JuanAVillagomez/FPGA-Retro-Arcade-Console/hardware/Retro_KiCAD.kicad_sch

## KiCad design hardware/Retro_KiCAD.kicad_sch (2026-09-01)

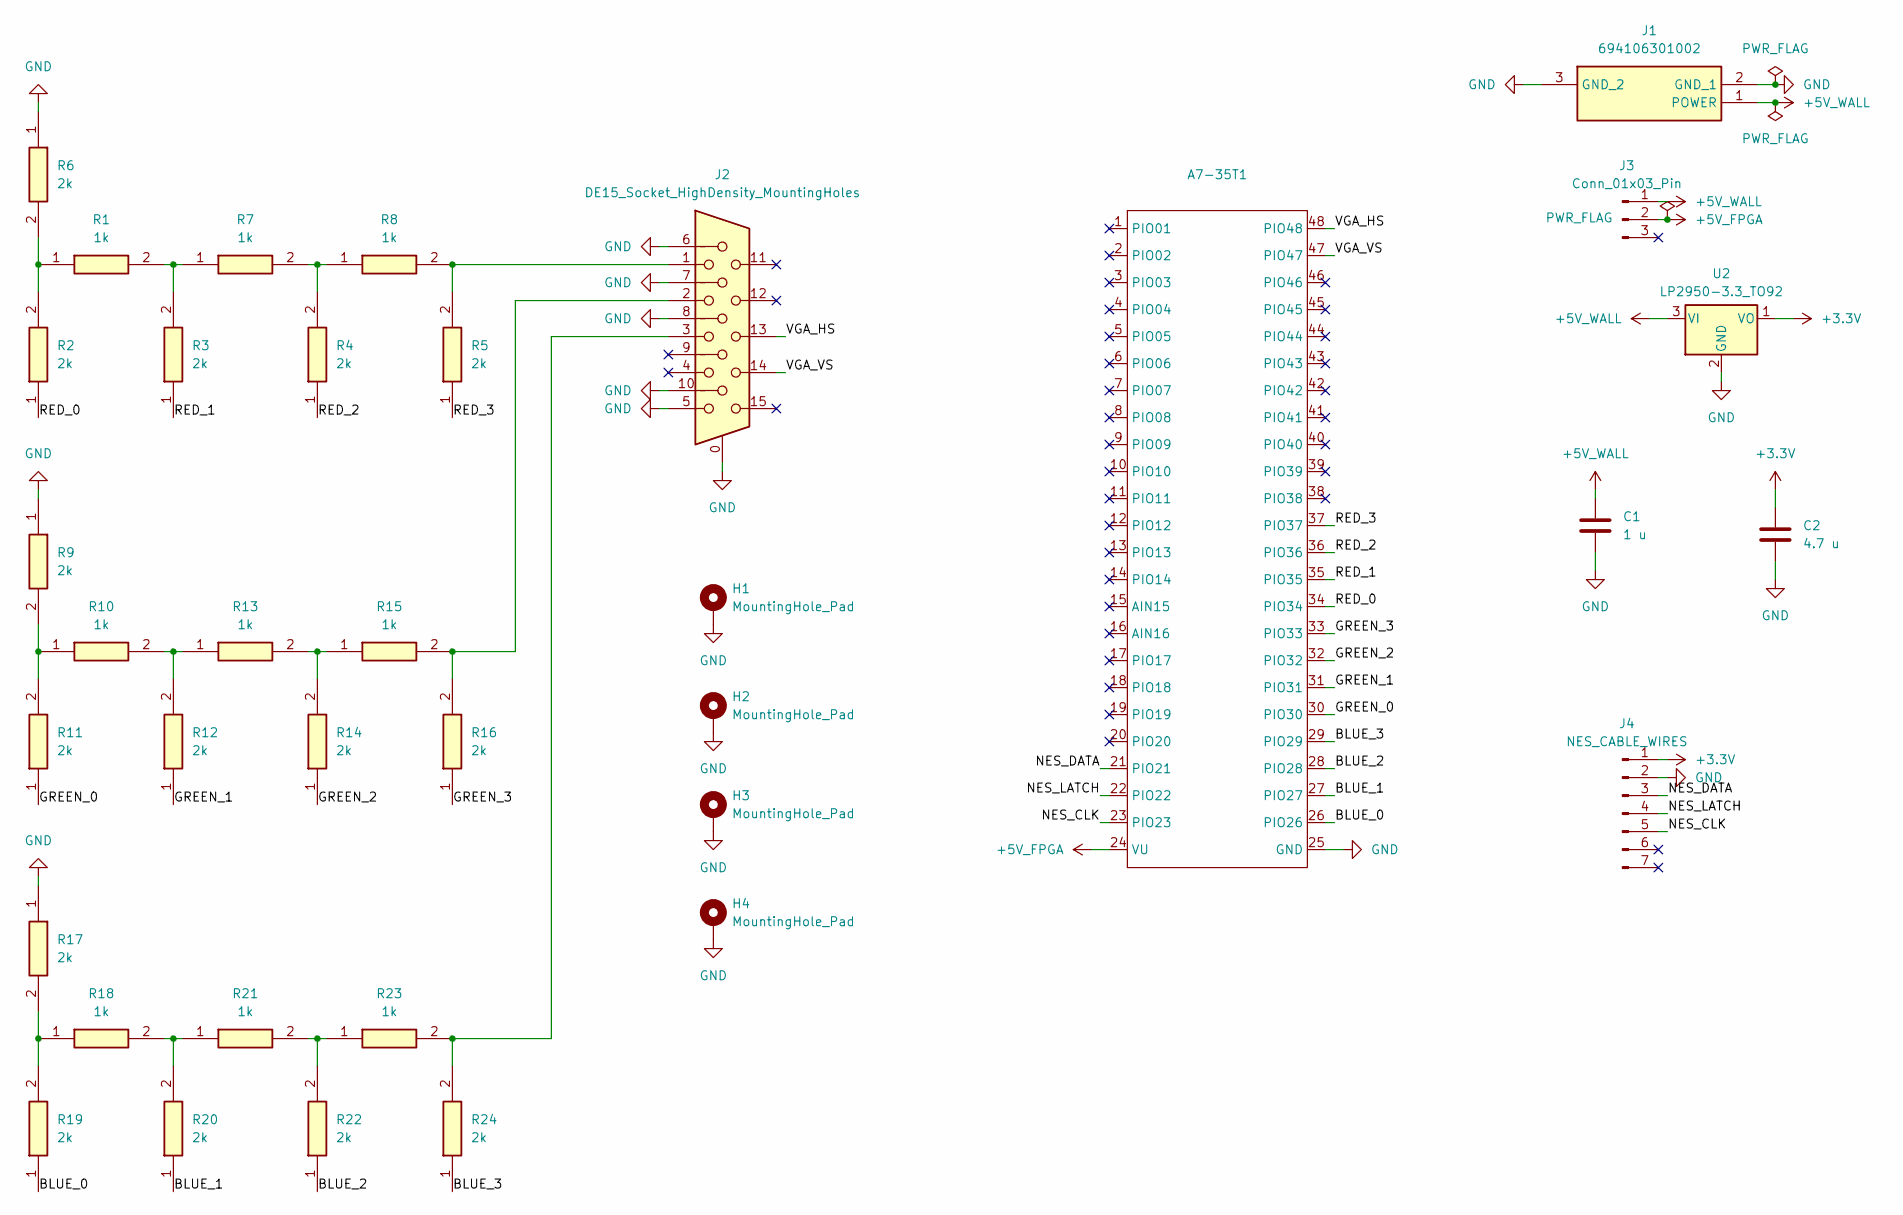
[picture p8: schematic Retro_KiCAD.kicad_sch]

Parts:
A7-35T1: DIP-48_600mil
C1: 1 u; C_0805_2012Metric
C2: 4.7 u; C_0805_2012Metric
H1, H2, H3, H4: MountingHole_Pad; MountingHole_3.2mm_M3_Pad_Via
J1: 694106301002; BarrelJack_Wuerth_6941xx301002; Mouser Part Number 710-694106301002
J2: DE15_Socket_HighDensity_MountingHoles; DSUB-15-HD_Socket_Horizontal_P2.29x1.90mm_EdgePinOffset3.03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
J3: Conn_01x03_Pin; PinHeader_1x03_P2.54mm_Vertical
J4: NES_CABLE_WIRES; PinHeader_1x07_P2.54mm_Vertical
R1, R7, R8, R10, R13, R15, R18, R21, R23: 1k; R_0805_2012Metric; Mouser Part Number 66-WCR0805LF1001FPLT
R2, R3, R4, R5, R6, R9, R11, R12, R14, R16, R17, R19, R20, R22, R24: 2k; R_0805_2012Metric; Mouser Part Number 667-ERJ-U06F2001V
U2: LP2950-3.3_TO92; TO-92_Inline

Connections:
+3.3V: C2.1, J4.1, U2.1 (VO)
+5V_FPGA: A7-35T1.24 (VU), J3.2
+5V_WALL: C1.1, J1.1 (POWER), J3.1, U2.3 (VI)
BLUE_0: A7-35T1.26 (PIO26), R19.1
BLUE_1: A7-35T1.27 (PIO27), R20.1
BLUE_2: A7-35T1.28 (PIO28), R22.1
BLUE_3: A7-35T1.29 (PIO29), R24.1
GND: A7-35T1.25 (GND), C1.2, C2.2, H1.1, H2.1, H3.1, H4.1, J1.2 (GND_1), J1.3 (GND_2), J2.0, J2.5, J2.6, J2.7, J2.8, J2.10, J4.2, R6.1, R9.1, R17.1, U2.2 (GND)
GREEN_0: A7-35T1.30 (PIO30), R11.1
GREEN_1: A7-35T1.31 (PIO31), R12.1
GREEN_2: A7-35T1.32 (PIO32), R14.1
GREEN_3: A7-35T1.33 (PIO33), R16.1
NES_CLK: A7-35T1.23 (PIO23), J4.5
NES_DATA: A7-35T1.21 (PIO21), J4.3
NES_LATCH: A7-35T1.22 (PIO22), J4.4
unnamed: J2.1, R5.2, R8.2
unnamed: J2.2, R15.2, R16.2
unnamed: J2.3, R23.2, R24.2
unnamed: R1.1, R2.2, R6.2
unnamed: R1.2, R3.2, R7.1
unnamed: R4.2, R7.2, R8.1
unnamed: R9.2, R10.1, R11.2
unnamed: R10.2, R12.2, R13.1
unnamed: R13.2, R14.2, R15.1
unnamed: R17.2, R18.1, R19.2
unnamed: R18.2, R20.2, R21.1
unnamed: R21.2, R22.2, R23.1
RED_0: A7-35T1.34 (PIO34), R2.1
RED_1: A7-35T1.35 (PIO35), R3.1
RED_2: A7-35T1.36 (PIO36), R4.1
RED_3: A7-35T1.37 (PIO37), R5.1
VGA_HS: A7-35T1.48 (PIO48), J2.13
VGA_VS: A7-35T1.47 (PIO47), J2.14
